TheNitek/RfidShelf/images/board/x_audioadapter.jpg

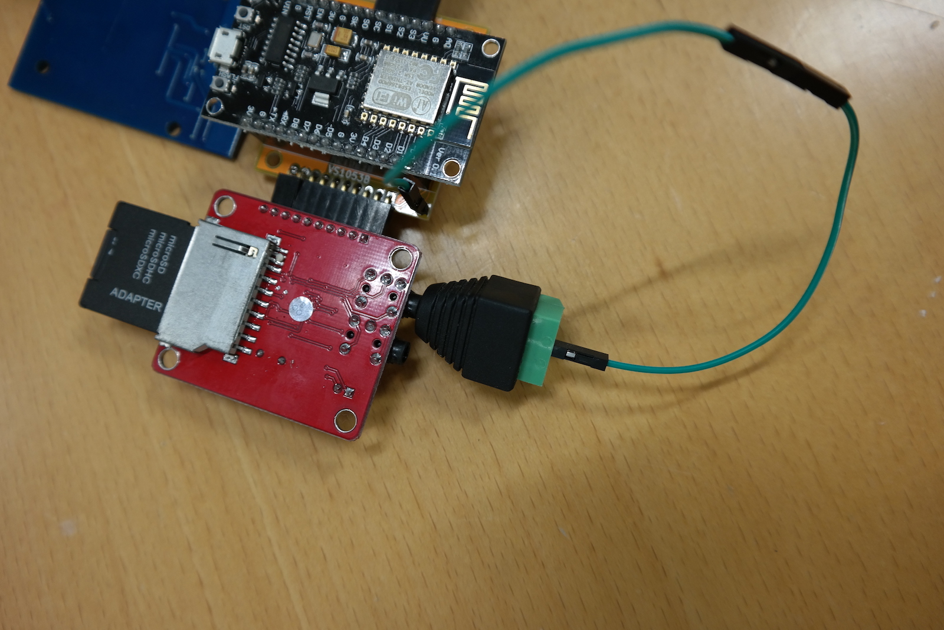
images/board/x_audioadapter.jpg
