TheNitek/RfidShelf/images/board/x_boardbottom.jpg

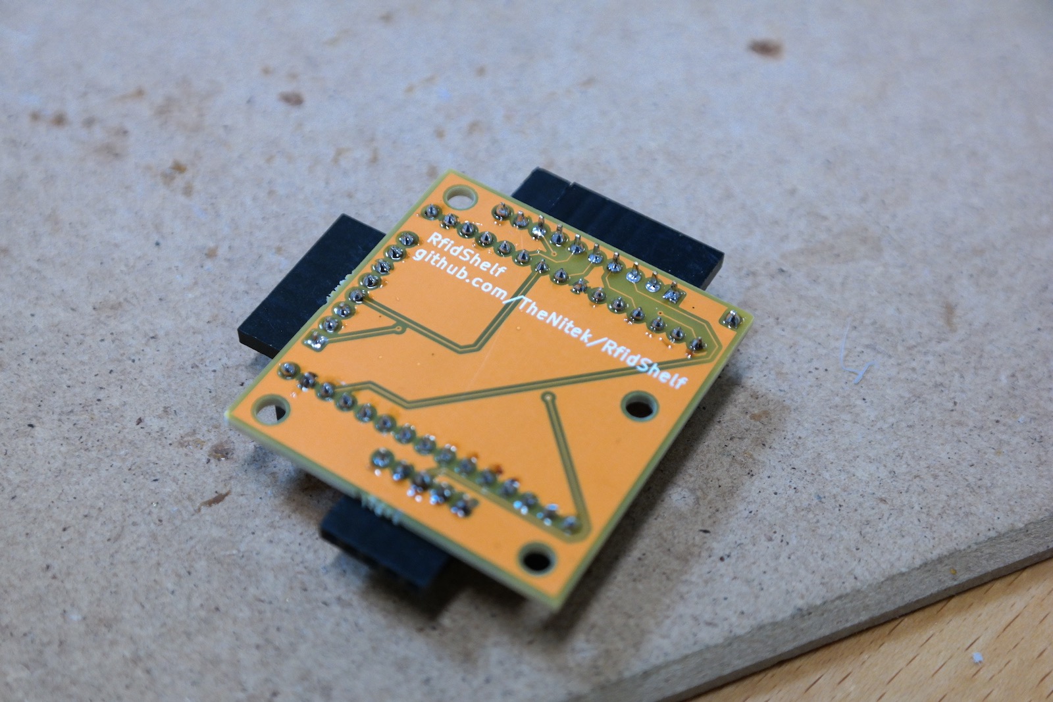
images/board/x_boardbottom.jpg
