TheNitek/RfidShelf/images/board/x_boardsbottom.jpg

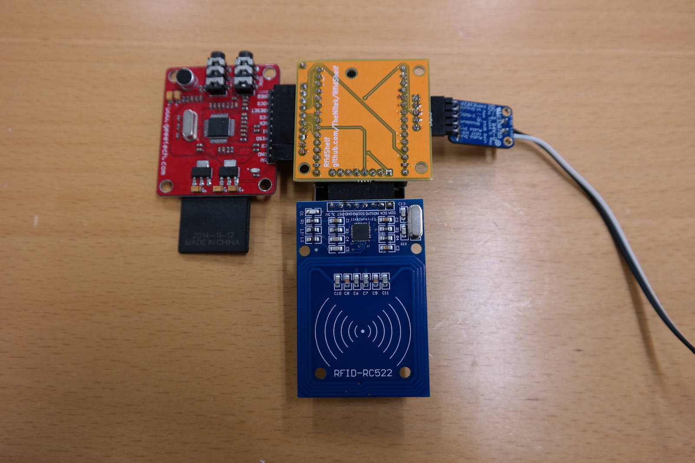
images/board/x_boardsbottom.jpg
