TheNitek/RfidShelf/images/board/x_boardstop.jpg

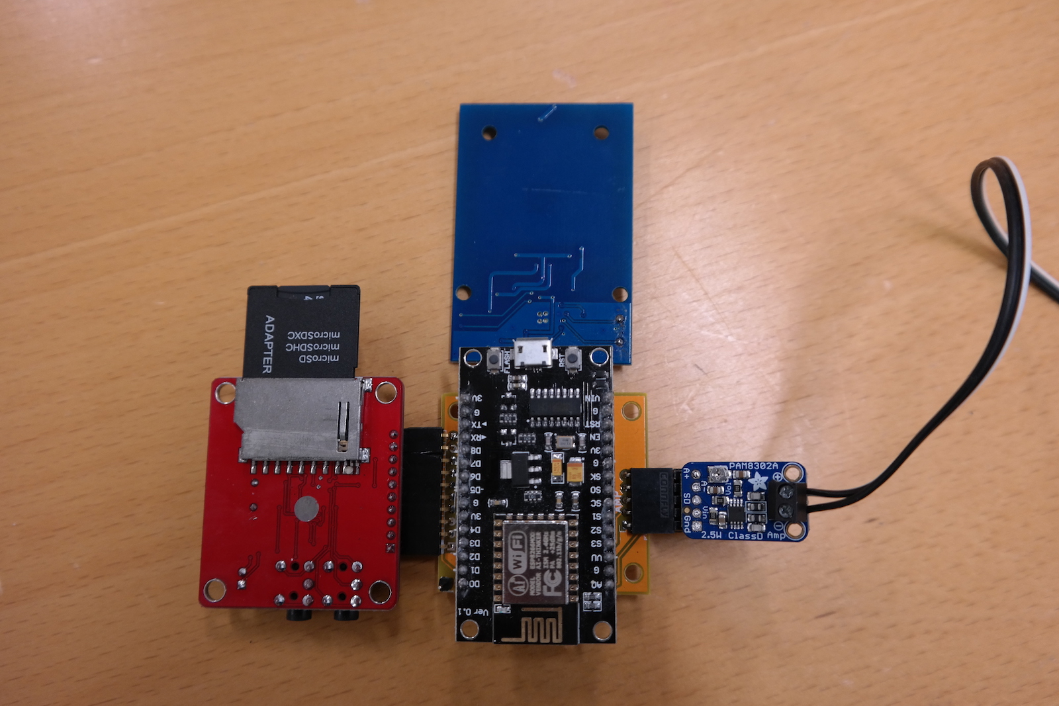
images/board/x_boardstop.jpg
