TheNitek/RfidShelf/images/board/x_boardtop.jpg

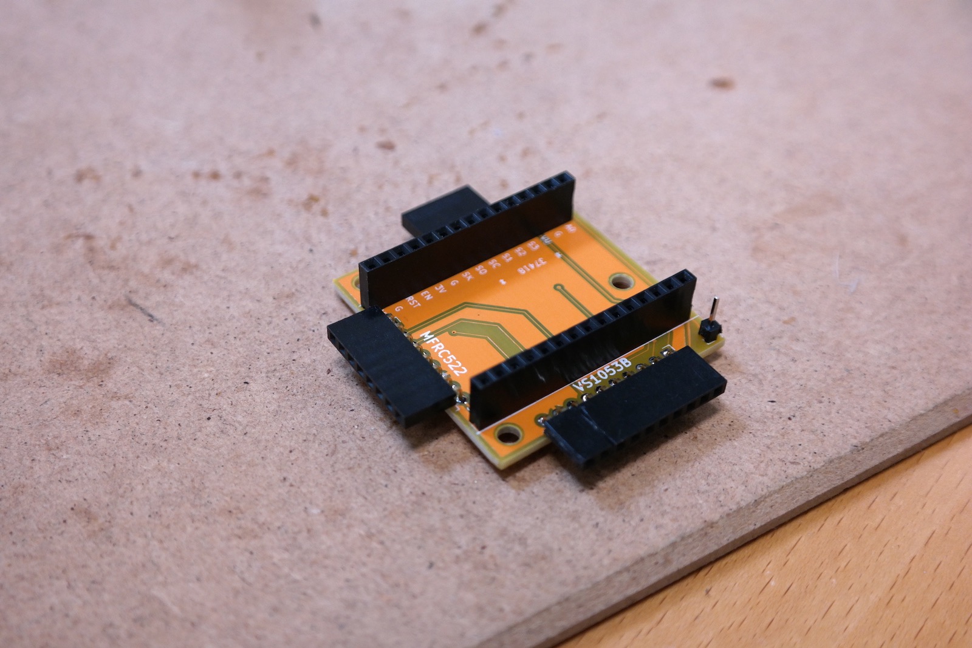
images/board/x_boardtop.jpg
