TheNitek/RfidShelf/images/board/x_audiosolder.jpg

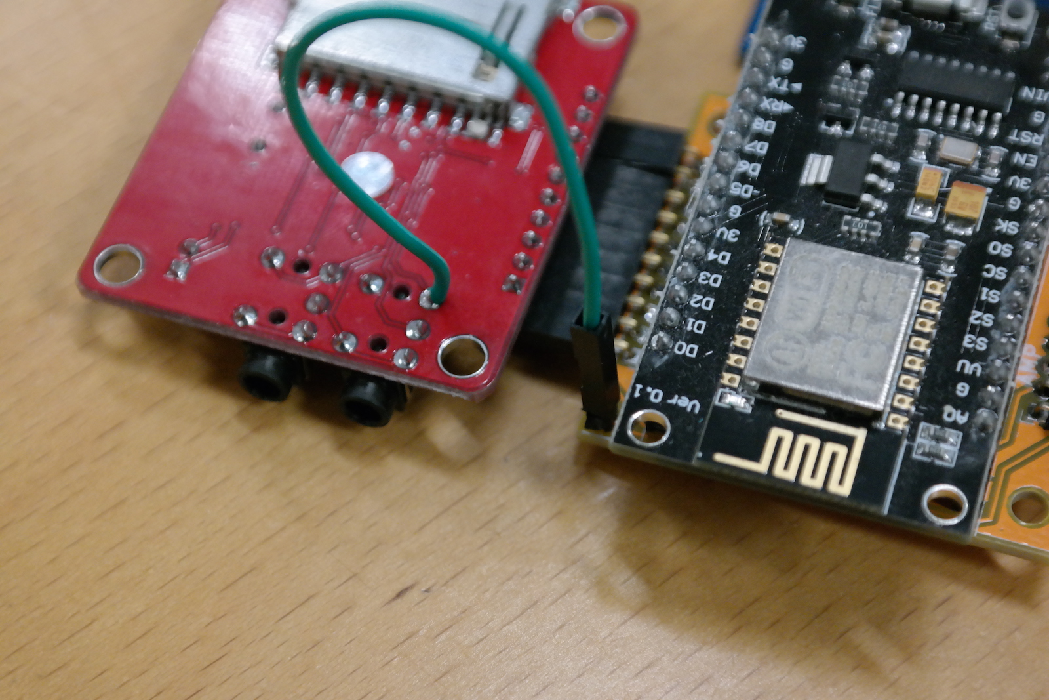
images/board/x_audiosolder.jpg
