TheNitek/RfidShelf/RfidShelf/src/ShelfRfid.cpp

#include "ShelfRfid.h"

void ShelfRfid::begin() {
  _mfrc522.PCD_Init(); // Init MFRC522 card

  Sprintln(F("RFID initialized"));
}

void ShelfRfid::handleRfid(bool ignoreTagData) {
  if ((_playback.playbackState() != ShelfPlayback::PLAYBACK_NO) && (millis() - _lastRfidCheck < 500)) {
    return;
  }
  _lastRfidCheck = millis();

  // While playing check if the tag is still present
  if ((_playback.playbackState() == ShelfPlayback::PLAYBACK_FILE)
      && _playback.playingByCard
      && (_currentCard.config.stopOnRemove == 1 || (_currentCard.config.stopOnRemove == 2 && _config.defaultStopOnRemove))) {

    // Since wireless communication is voodoo we'll give it a few retrys before killing the music
    for (int i = 0; i < 3; i++) {
      // Detect Tag without looking for collisions
      byte bufferATQA[2];
      byte bufferSize = sizeof(bufferATQA);

      MFRC522::StatusCode result = _mfrc522.PICC_WakeupA(bufferATQA, &bufferSize);

      if (result == MFRC522::STATUS_OK && _mfrc522.PICC_ReadCardSerial() && !memcmp(_mfrc522.uid.uidByte, _lastCardUid, 4)) {
        _mfrc522.PICC_HaltA();
        return;
      }
    }

    _playback.pausePlayback();
  }

  // Look for new cards and select one if it exists
  if (!_mfrc522.PICC_IsNewCardPresent() ||  !_mfrc522.PICC_ReadCardSerial()) {
    return;
  }

  if(ignoreTagData) {
    Sprintln(F("Ignoring current tag"));
    // Halt PICC
    _mfrc522.PICC_HaltA();
    // Stop encryption on PCD
    _mfrc522.PCD_StopCrypto1();
    return;
  }

  // Show some details of the PICC (that is: the tag/card)
  Sprint(F("Card UID:"));
  _print_byte_array(_mfrc522.uid.uidByte, _mfrc522.uid.size);
  Sprint(F("PICC type: "));
  MFRC522::PICC_Type piccType = _mfrc522.PICC_GetType(_mfrc522.uid.sak);
  Sprintln(_mfrc522.PICC_GetTypeName(piccType));

  // Check for compatibility
  if (piccType != MFRC522::PICC_TYPE_MIFARE_1K && piccType != MFRC522::PICC_TYPE_MIFARE_UL ) {
    Sprintln(F("Unsupported card."));
    return;
  }

  if (hasActivePairing) {
    _playback.stopPlayback();
    _writeRfidBlock(1, 0, (uint8_t*) _pairingCard.folder, strlen(_pairingCard.folder)+1);
    _writeConfigBlock(&_pairingCard.config);
    hasActivePairing = false;
  }

  // Reset watchdog timer
  ESP.wdtFeed();
  _handleRfidData();

  // Halt PICC
  _mfrc522.PICC_HaltA();
  // Stop encryption on PCD
  _mfrc522.PCD_StopCrypto1();
}

void ShelfRfid::_handleRfidData() {
  uint8_t readBuffer[18];
  /* RFID Layout:
   * Mifare Classic:
   * Sector 1, Block 0: Folder
   * Sector 2, Block 0: Config
   * 
   * Mifare Ultra:
   * Page 4-7: Folder
   * Page 8-11: Config
  */
  if (!_readRfidBlock(1, 0, readBuffer, sizeof(readBuffer))) {
    // we could not read card, skip handling
    return;
  }

  // Store uid
  memcpy(_lastCardUid, _mfrc522.uid.uidByte, 4 * sizeof(uint8_t) );

  if(readBuffer[0] == '\0') {
    return;
  }

  char readFolder[18];
  readFolder[0] = '/';
  // allthough sizeof(readBuffer) == 18, we only get 16 byte of data (2 bytes are CRC)
  memcpy(readFolder + 1 , readBuffer, 16 * sizeof(uint8_t) );
  // readBuffer will already contain \0 if the folder name is < 16 chars, but otherwise we need to add it
  readFolder[17] = '\0';

  char currentFolder[101];
  currentFolder[0] = '/';
  _playback.currentFolder(currentFolder+1, sizeof(currentFolder)-1);
  if ((_playback.playbackState() != ShelfPlayback::PLAYBACK_NO) && !strcmp(readFolder, currentFolder)) {
    Sprint(F("Resuming ")); Sprintln(currentFolder);
    _playback.resumePlayback();
    _playback.playingByCard = true;
  } else if (_playback.switchFolder(readFolder) && _handleRfidConfig()) {
    strcpy(_currentCard.folder, readFolder);
    _setPlaybackOptions(_currentCard.config.repeat, _currentCard.config.shuffle);
    _playback.startPlayback();
    _playback.playingByCard = true;
  } else {
    Sprintln(F("Ignoring card"));
    return;
  }

  _dumpCurrentCard(&_currentCard);
}

bool ShelfRfid::_handleRfidConfig() {
  uint8_t configBuffer[18];
  if (!_readRfidBlock(2, 0, configBuffer, sizeof(configBuffer))) {
    // we could not read card config, skip handling
    return false;
  }

  memcpy(&_currentCard.config, configBuffer, sizeof(CardConfig));

  if(_currentCard.config.magicByte != RFID_CONFIG_MARKER || _currentCard.config.size != 2) {
    // "Upgrade" card
    Sprintln(F("Found old version, upgrading card..."));
    _currentCard.config.size = 2;
    _currentCard.config.repeat = 2;
    _currentCard.config.shuffle = 2;
    _currentCard.config.stopOnRemove = 2;
    if(_currentCard.config.magicByte != RFID_CONFIG_MARKER || _currentCard.config.size != 1) {
      Sprintln(F("Setting magic byte and volume"));
      _currentCard.config.magicByte = RFID_CONFIG_MARKER;
      _currentCard.config.volume = _config.defaultVolumne;
    }
    _writeConfigBlock(&_currentCard.config);
  }

  Sprint(F("Setting volume: ")); Sprintln(_currentCard.config.volume);
  _playback.volume(_currentCard.config.volume);
  return true;
}


void ShelfRfid::_setPlaybackOptions(const uint8_t repeat, const uint8_t shuffle) {
  if(repeat == 1 || (repeat == 2 && _config.defaultRepeat)) {
    _playback.startRepeat();
  } else {
    _playback.stopRepeat();
  }
  
  if(shuffle == 1 || (shuffle == 2 && _config.defaultShuffle)) {
    _playback.startShuffle();
  } else {
    _playback.stopShuffle();
  }
}

ShelfRfid::NFCTagObject ShelfRfid::getPairingConfig() {
  return _pairingCard;
}

bool ShelfRfid::startPairing(const char *folder, const uint8_t volume, const uint8_t repeat, const uint8_t shuffle, const uint8_t stopOnRemove) {
  if(strlen(folder) > 16 || repeat > 2 || shuffle > 2 || stopOnRemove > 2)
    return false;
  
  strcpy(_pairingCard.folder, folder);
  _pairingCard.config.magicByte = RFID_CONFIG_MARKER;
  _pairingCard.config.size = 2;
  _pairingCard.config.volume = volume;
  _pairingCard.config.repeat = repeat;
  _pairingCard.config.shuffle = shuffle;
  _pairingCard.config.stopOnRemove = stopOnRemove;

  Sprintln(F("Pairing mode enabled"));
  _dumpCurrentCard(&_pairingCard);

  hasActivePairing = true;
  return true;
}

void ShelfRfid::_dumpCurrentCard(const NFCTagObject *card) {
  Sprintln(F("Current card data: "));
  Sprint(F("  folder: ")); Sprintln(card->folder);
  Sprint(F("  volume: ")); Sprintln(card->config.volume);
  Sprint(F("  repeat: ")); Sprintln(card->config.repeat);
  Sprint(F("  shuffle: ")); Sprintln(card->config.shuffle);
  Sprint(F("  stopOnRemove: ")); Sprintln(card->config.stopOnRemove);
}

void ShelfRfid::_writeConfigBlock(const CardConfig *config) {

  // Store config (like volume)
  uint8_t configBuffer[sizeof(CardConfig)];

  memcpy(configBuffer, config, sizeof(CardConfig));
  _writeRfidBlock(2, 0, configBuffer, sizeof(CardConfig));
}

bool ShelfRfid::_writeRfidBlock(const uint8_t sector, const uint8_t relativeBlock, const uint8_t *content, const uint8_t contentSize) {
  uint8_t absoluteBlock = (sector * 4) + relativeBlock;
  MFRC522::StatusCode status;
  MFRC522::PICC_Type piccType = _mfrc522.PICC_GetType(_mfrc522.uid.sak);

  if(piccType == MFRC522::PICC_TYPE_MIFARE_1K) {
      // Authenticate using key A
    Sprintln(F("Authenticating using key A..."));
    status = _mfrc522.PCD_Authenticate(MFRC522::PICC_CMD_MF_AUTH_KEY_A, absoluteBlock, &_key, &(_mfrc522.uid));
    if (status != MFRC522::STATUS_OK) {
      Sprint(F("PCD_Authenticate() failed: "));
      Sprintln(_mfrc522.GetStatusCodeName(status));
      return false;
    }
  }

  const uint8_t bufferSize = 16;
  byte buffer[bufferSize];

  uint8_t blockSize = 16;
  if(piccType == MFRC522::PICC_TYPE_MIFARE_UL) {
    blockSize = 4;
  }

  // While reading works basically the same for Mifare Classic and Ultra, Ultras need to be written in chunks of 4 bytes instead of 16
  Sprint(F("Writing data: ")); _print_byte_array(content, contentSize);
  for(uint8_t i = 0; (i < 16/blockSize) && (i*blockSize < contentSize); i++) {
    // Write block
    memset(buffer, 0, bufferSize * sizeof(uint8_t));
    memcpy(buffer, content+(i*blockSize), (((i+1)*blockSize > contentSize) ? (contentSize % blockSize) : blockSize) * sizeof(uint8_t) );

    status = _mfrc522.MIFARE_Write(absoluteBlock + i, buffer, bufferSize);
    if (status != MFRC522::STATUS_OK) {
      Sprint(F("MIFARE_Write() failed: ")); Sprintln(_mfrc522.GetStatusCodeName(status));
      return false;
    }
  }
  return true;
}

/**
   read a block from a rfid card into outputBuffer which needs to be >= 18 bytes long
*/
bool ShelfRfid::_readRfidBlock(uint8_t sector, uint8_t relativeBlock, uint8_t *outputBuffer, uint8_t bufferSize) {
  if (relativeBlock > 3) {
    Sprintln(F("Invalid block number"));
    return false;
  }

  uint8_t absoluteBlock = (sector * 4) + relativeBlock;
  MFRC522::StatusCode status;
  MFRC522::PICC_Type piccType = _mfrc522.PICC_GetType(_mfrc522.uid.sak);

  if(piccType == MFRC522::PICC_TYPE_MIFARE_1K) {
    // Authenticate using key A
    Sprintln(F("Authenticating using key A..."));
    status = _mfrc522.PCD_Authenticate(MFRC522::PICC_CMD_MF_AUTH_KEY_A, absoluteBlock, &_key, &(_mfrc522.uid));
    if (status != MFRC522::STATUS_OK) {
      Sprint(F("PCD_Authenticate() failed: "));
      Sprintln(_mfrc522.GetStatusCodeName(status));
      return false;
    }
  }

  Sprint(F("Reading block ")); Sprint(absoluteBlock); Sprintln(F(":"));
  status = _mfrc522.MIFARE_Read(absoluteBlock, outputBuffer, &bufferSize);
  if (status != MFRC522::STATUS_OK) {
    Sprint(F("MIFARE_Read() failed: ")); Sprintln(_mfrc522.GetStatusCodeName(status));
    return false;
  }
  _print_byte_array(outputBuffer, 16);
  Sprintln();
  Sprintln();

  return true;
}


void ShelfRfid::_print_byte_array(const uint8_t *buffer, const uint8_t  bufferSize) {
#ifdef DEBUG_ENABLE
  for (uint8_t i = 0; i < bufferSize; i++) {
    Sprint(buffer[i] < 0x10 ? " 0" : " ");
    // Use Serial.print here because of HEX parameter and ifdef around this
    Serial.print(buffer[i], HEX);
  }
  Sprintln();
#endif
}
