TheNitek/RfidShelf/RfidShelf/ShelfWeb.cpp

#include "ShelfWeb.h"

void ShelfWeb::begin() {
  std::function<void(void)> defaultCallback = std::bind(&ShelfWeb::_handleDefault, this);
  _server.on(
    "/",
    HTTP_POST,
    defaultCallback,
    std::bind(&ShelfWeb::_handleFileUpload, this)
  );
  _server.onNotFound(defaultCallback);
  // Done by espalexa
  //_server.begin();

  DeviceCallbackFunction deviceCallback = std::bind(&ShelfWeb::_deviceCallback, this, std::placeholders::_1);
  _alexaDevice = new EspalexaDevice(_config.hostname, deviceCallback, EspalexaDeviceType::dimmable, 50);
  _alexaDevice->setPercent(2*(50-_playback.volume()));
  _espalexa.addDevice(_alexaDevice);
  _espalexa.begin(&_server);

  PlaybackCallbackFunction playbackCallback = std::bind(&ShelfWeb::_playbackCallback, this, std::placeholders::_1, std::placeholders::_2);
  _playback.callback = playbackCallback;

  MDNS.addService("http", "tcp", 80);
}

void ShelfWeb::_deviceCallback(EspalexaDevice* device) {
  Sprintf("Got device callback type: %d\n", device->getLastChangedProperty());

  switch(device->getLastChangedProperty()) {
    case EspalexaDeviceProperty::off:
      if(_playback.playbackState() == PLAYBACK_FILE) {
        _playback.pausePlayback();
      }
      break;
    case EspalexaDeviceProperty::on: 
      if(_playback.playbackState() == PLAYBACK_PAUSED) {
        _playback.playingByCard = false;
        _playback.resumePlayback();
        device->setPercent(2*(50-_playback.volume()));
      }
      break;
    case EspalexaDeviceProperty::bri:
      _playback.volume(50-device->getPercent()/2, false);
      break;
    default:
      Sprintln("Callback ignored");
  }
}

void ShelfWeb::_playbackCallback(PlaybackState state, uint8_t volume) {
  if(state == PLAYBACK_FILE) {
    _alexaDevice->setPercent(2*(50-_playback.volume()));
  } else {
    _alexaDevice->setValue(0);
  }
}

void ShelfWeb::_returnOK() {
  _server.send_P(200, "text/plain", NULL);
}

void ShelfWeb::_returnHttpStatus(uint16_t statusCode, const char *msg) {
  _server.send_P(statusCode, "text/plain", msg);
}

void ShelfWeb::_sendHTML() {
  _server.sendHeader("Content-Encoding", "gzip");
  _server.send_P(200, "text/html", ShelfHtml::INDEX, ShelfHtml::INDEX_SIZE);
}

void ShelfWeb::_sendJsonStatus() {
  char output[768] = "{\"playback\":\"";
  char buffer[101];

  if(_playback.playbackState() == PLAYBACK_FILE) {
    strcat(output, "FILE\"");
  } else if(_playback.playbackState() == PLAYBACK_PAUSED) {
    strcat(output, "PAUSED\"");
  } else {
    strcat(output, "NO\"");
  }

  if(_rfid.hasActivePairing) {
    nfcTagObject pairingConfig = _rfid.getPairingConfig();
    strcat(output, ",\"pairing\":\"");
    strcat(output, pairingConfig.folder);
    strcat(output, "\"");
  }

  if(_playback.playbackState() != PLAYBACK_NO) {
    _playback.currentFile(buffer, sizeof(buffer));
    strcat(output, ",\"currentFile\":\"");
    strcat(output, buffer);
    _playback.currentFolder(buffer, sizeof(buffer));
    strcat(output, "\",\"currentFolder\":\"");
    strcat(output, buffer);
    strcat(output, "\"");
  }

  strcat(output, ",\"volume\":");
  snprintf(buffer, sizeof(buffer), "%d", 50 - _playback.volume());
  strcat(output, buffer);

  if (_SD.exists("/patches.053")) {
    strcat(output, ",\"patch\":true");
  } else {
    strcat(output, ",\"patch\":false");
  }

  if(_playback.isNight()) {
    strcat(output, ",\"night\":true");
  } else {
    strcat(output, ",\"night\":false");
  }

  if(_playback.isShuffle()) {
    strcat(output, ",\"shuffle\":true");
  } else {
    strcat(output, ",\"shuffle\":false");
  }

  strcat(output, ",\"time\":");
  snprintf(buffer, sizeof(buffer), "%lu", time(nullptr));
  strcat(output, buffer);

  strcat(output, ",\"version\":");
  snprintf(buffer, sizeof(buffer), "\"%d.%d\"", MAJOR_VERSION, MINOR_VERSION);
  strcat(output, buffer);
  strcat(output, "}");

  _server.send_P(200, "application/json", output);
}

void ShelfWeb::_sendJsonFSUsage() {
  uint32_t free = (uint32_t)(0.000512*_SD.vol()->freeClusterCount()*_SD.vol()->blocksPerCluster());
  uint32_t total = (uint32_t)(0.000512*_SD.card()->cardCapacity());

  // This is too slow on bigger cards, so it needs to be moved somewhere else
  char output[51] = "";
  snprintf(output, sizeof(output), "{\"free\":%u,\"total\":%u}", free, total);
  _server.send_P(200, "application/json", output);
}

void ShelfWeb::_sendJsonConfig() {
  char output[768] = "{\"host\":\"";
  char buffer[101];

  strcat(output, _config.hostname);
  strcat(output, "\",\"ntp\":\"");
  strcat(output, _config.ntpServer);
  strcat(output, "\",\"tz\":\"");
  strcat(output, _config.timezone);
  strcat(output, "\",\"volume\":");
  snprintf(buffer, sizeof(buffer), "%d", _config.defaultVolumne);
  strcat(output, buffer);
  strcat(output, ",\"repeat\":");
  strcat(output, _config.defaultRepeat ? "true" : "false");
  strcat(output, ",\"shuffle\":");
  strcat(output, _config.defaultShuffle ? "true" : "false");
  strcat(output, ",\"stopOnRemove\":");
  strcat(output, _config.defaultStopOnRemove ? "true" : "false");
  strcat(output, ",\"nightMode\":[");
  for(uint8_t i = 0; i < sizeof(_config.nightModeTimes)/sizeof(Timeslot_t); i++) {
    strcat(output, "{");
    strcat(output, "\"days\":[");
    strcat(output, _config.nightModeTimes[i].monday ? "true," : "false,");
    strcat(output, _config.nightModeTimes[i].tuesday ? "true," : "false,");
    strcat(output, _config.nightModeTimes[i].wednesday ? "true," : "false,");
    strcat(output, _config.nightModeTimes[i].thursday ? "true," : "false,");
    strcat(output, _config.nightModeTimes[i].friday ? "true," : "false,");
    strcat(output, _config.nightModeTimes[i].saturday ? "true," : "false,");
    strcat(output, _config.nightModeTimes[i].sunday ? "true" : "false");
    strcat(output, "],\"start\":\"");
    snprintf(buffer, sizeof(buffer), "%02d:%02d", _config.nightModeTimes[i].startHour, _config.nightModeTimes[i].startMinutes);
    strcat(output, buffer);
    strcat(output, "\",\"end\":\"");
    snprintf(buffer, sizeof(buffer), "%02d:%02d", _config.nightModeTimes[i].endHour, _config.nightModeTimes[i].endMinutes);
    strcat(output, buffer);
    strcat(output, "\"");

    strcat(output, "}");
    if(i < sizeof(_config.nightModeTimes)/sizeof(Timeslot_t) - 1) {
      strcat(output, ",");
    }
  }
  strcat(output, "]}");

  _server.send_P(200, "application/json", output);
}

void ShelfWeb::_sendJsonFS(const char *path) {
  _server.setContentLength(CONTENT_LENGTH_UNKNOWN);
  _server.send_P(200, "application/json", "{\"fs\":[");

  sdfat::SdFile dir;
  dir.open(path, sdfat::O_READ);

  sdfat::SdFile entry;

  char buffer[101];
  char output[256];

  bool first = true;

  while (entry.openNext(&dir, sdfat::O_READ)) {
    if(first) {
      first = false;
      strcpy(output, "{\"name\":\"");
    } else {
      strcpy(output, ",{\"name\":\"");
    }
    entry.getName(buffer, sizeof(buffer));
    // TODO encode special characters
    strcat(output, buffer);
    if (entry.isDir()) {
      strcat(output, "\"");
    } else {
      strcat(output, "\",\"size\":");
      snprintf(buffer, sizeof(buffer), "%lu", (unsigned long) entry.fileSize());
      strcat(output, buffer);
    }
    entry.close();
    strcat(output, "}");
    _server.sendContent_P(output);
  }
  _server.sendContent_P("],");
  snprintf(output, sizeof(output), "\"path\":\"%s\"", path);
  _server.sendContent_P(output);
  _server.sendContent_P("}");
  _server.sendContent_P("");

  dir.close();
}

bool ShelfWeb::_loadFromSdCard(const char *path) {
  sdfat::File dataFile = _SD.open(path);

  if (!dataFile) {
    Sprintln("File not open");
    _returnHttpStatus(404, "Not found");
    return false;
  }

  if (dataFile.isDir()) {
    _sendJsonFS(path);
  } else {
    if (_server.streamFile(dataFile, "application/octet-stream") != dataFile.size()) {
      Sprintln("Sent less data than expected!");
    }
  }
  dataFile.close();
  return true;
}

void ShelfWeb::_downloadPatch() {
  Sprintln("Starting patch download");
  std::unique_ptr<BearSSL::WiFiClientSecure>client(new BearSSL::WiFiClientSecure);
  // do not validate certificate
  client->setInsecure();
  HTTPClient httpClient;
  httpClient.begin(*client, VS1053_PATCH_URL);
  int httpCode = httpClient.GET();
  if (httpCode < 0) {
    httpClient.end();
    _returnHttpStatus(500, httpClient.errorToString(httpCode).c_str());
    return;
  }
  if (httpCode != HTTP_CODE_OK) {
    httpClient.end();
    char buffer[32];
    snprintf(buffer, sizeof(buffer), "invalid response code: %d", httpCode);
    _returnHttpStatus(500, buffer);
    return;
  }

  sdfat::File patchFile("/patches.053",sdfat::O_WRITE | sdfat::O_CREAT);
  if(!patchFile.isOpen()) {
    httpClient.end();
    _returnHttpStatus(500, "Could not open patch file");
    return;
  }
  patchFile.close();
  _returnOK();
  _server.client().flush();
  ESP.restart();
}

void ShelfWeb::_handleFileUpload() {
  // Upload always happens on /
  if (_server.uri() != "/") {
    Sprintln("Invalid upload URI");
    return;
  }

  HTTPUpload& upload = _server.upload();

  if (upload.status == UPLOAD_FILE_START) {
    String filename = upload.filename;

    if (!filename.startsWith("/")) {
      Sprintln("Invalid upload target");
      return;
    }

    if (_SD.exists(filename.c_str())) {
      Sprintln("File " + filename + " already exists. Skipping");
      return;
    }

    if(_playback.playbackState() == PLAYBACK_FILE) {
      Sprintln("Pausing playback for upload");
      _playback.pausePlayback();
    }

    _uploadFile.open(filename.c_str(), sdfat::O_WRITE | sdfat::O_CREAT);
    _uploadStart = millis();
    Sprint("Upload start: ");
    Sprintln(filename);
  } else if (upload.status == UPLOAD_FILE_WRITE) {
    if (_uploadFile.isOpen()) {
      _uploadFile.write(upload.buf, upload.currentSize);
      //Sprint("Upload write: "));
      //Sprintln(upload.currentSize);
    }
  } else if (upload.status == UPLOAD_FILE_END) {
    if (_uploadFile.isOpen()) {
      _uploadFile.close();
      Sprint("Upload end: "); Sprintln(upload.totalSize);
      Sprint("Took: "); Sprintln(((millis()-_uploadStart)/1000));
    }
  }
}

void ShelfWeb::_handleDefault() {
  String path = _server.urlDecode(_server.uri());
  Sprintf("Request to: %s\n", path.c_str());
  if(_espalexa.handleAlexaApiCall(_server.uri(), _server.arg("plain"))) {
    return;
  }
  if(_server.method() == HTTP_GET) {
    if(_server.hasArg("status")) {
      _sendJsonStatus();
      return;
    }
    if(_server.hasArg("config")) {
      _sendJsonConfig();
      return;
    }
    if(_server.hasArg("usage")) {
      _sendJsonFSUsage();
      return;
    }
    if(path == "/" && !_server.hasArg("fs")) {
      _sendHTML();
      return;
    }

    // start file download
    _loadFromSdCard(path.c_str());
    return;
  } else if(_server.method() == HTTP_DELETE) {
    if(path == "/" || !_SD.exists(path.c_str())) {
      _returnHttpStatus(400, "Bad path");
      return;
    }

    sdfat::SdFile file;
    file.open(path.c_str());
    if(file.isDir()) {
      if(!file.rmRfStar()) {
        Sprintln("Could not delete folder");
      }
    } else {
      if(!_SD.remove(path.c_str())) {
        Sprintln("Could not delete file");
      }
    }
    file.close();
    _returnOK();
    return;
  } else if(_server.method() == HTTP_POST) {
    if(_server.hasArg("newFolder")) {
      Sprint("Creating folder "); Sprintln(_server.arg("newFolder"));
      if(_SD.mkdir(_server.arg("newFolder").c_str())) {
        _SD.cacheClear();
        _returnOK();
      } else {
        Sprintln("Folder creation failed");
        _returnHttpStatus(500, "Folder creation failed");
      }
      return;
    } else if(_server.hasArg("ota")) {
      Sprint("Starting OTA from "); Sprintln(_server.arg("ota"));
      std::unique_ptr<BearSSL::WiFiClientSecure>client(new BearSSL::WiFiClientSecure);
      // do not validate certificate
      client->setInsecure();
      t_httpUpdate_return ret = ESPhttpUpdate.update(*client, _server.arg("ota"));
      switch (ret) {
        case HTTP_UPDATE_FAILED:
          Sprintf("HTTP_UPDATE_FAILD Error (%d): ", ESPhttpUpdate.getLastError());
          Sprintln(ESPhttpUpdate.getLastErrorString().c_str());
          _returnHttpStatus(500, "Update failed, please try again");
          return;
        case HTTP_UPDATE_NO_UPDATES:
          Sprintln("HTTP_UPDATE_NO_UPDATES");
          break;
        case HTTP_UPDATE_OK:
          Sprintln("HTTP_UPDATE_OK");
          break;
      }
      _returnOK();
      return;
    } else if(_server.hasArg("downloadpatch")) {
      _downloadPatch();
      return;
    } else if(_server.hasArg("stop")) {
      _playback.stopPlayback();
      _sendJsonStatus();
      return;
    } else if(_server.hasArg("pause")) {
      _playback.pausePlayback();
      _sendJsonStatus();
      return;
    } else if(_server.hasArg("resume")) {
      _playback.playingByCard = false;
      _playback.resumePlayback();
      _sendJsonStatus();
      return;
    } else if(_server.hasArg("skip")) {
      _playback.playingByCard = false;
      _playback.skipFile();
      _sendJsonStatus();
      return;
    } else if(_server.hasArg("volumeUp")) {
      _playback.volumeUp();
      _sendJsonStatus();
      return;
    } else if(_server.hasArg("volumeDown")) {
      _playback.volumeDown();
      _sendJsonStatus();
      return;
    } else if(_server.hasArg("toggleNight")) {
      if(_playback.isNight()) {
        _playback.stopNight();
      } else {
        _playback.startNight();
      }
      _sendJsonStatus();
      return;
    } else if(_server.hasArg("toggleShuffle")) {
      if(_playback.isShuffle()) {
        _playback.stopShuffle();
      } else {
        _playback.startShuffle();
      }
      _sendJsonStatus();
      return;
    } else if(_server.uri() == "/") {
      Sprintln("Probably got an upload request");
      _returnOK();
      return;
    } else if(_SD.exists(path.c_str())) {
      // <= 17 here because leading "/"" is included
      if(_server.hasArg("write") && path.length() <= 17) {
        const char *target = path.c_str();
        const uint8_t volume = 50-(uint8_t)_server.arg("volume").toInt();
        uint8_t repeat = _server.arg("repeat").toInt();
        uint8_t shuffle = _server.arg("shuffle").toInt();
        uint8_t stopOnRemove = _server.arg("stopOnRemove").toInt();
        // Remove leading "/""
        target++;
        if(_rfid.startPairing(target, volume, repeat, shuffle, stopOnRemove)) {
          _sendJsonStatus();
          return;
        }
      } else if(_server.hasArg("play") && _playback.switchFolder(path.c_str())) {
        _playback.startPlayback();
        _playback.playingByCard = false;
        _sendJsonStatus();
        return;
      } else if(_server.hasArg("playfile")) {
        char* pathCStr = (char *)path.c_str();
        char* folderRaw = strtok(pathCStr, "/");
        char* file = strtok(NULL, "/");

        if((folderRaw != NULL) && (file != NULL) && strlen(folderRaw) < 90) {

          char folder[100] = "/";
          strcat(folder, folderRaw);
          strcat(folder, "/");

          if(_playback.switchFolder(folder)) {
            _playback.startFilePlayback(folderRaw, file);
            _playback.playingByCard = false;
            _sendJsonStatus();
            return;
          }
        }
      }
    }
  }

  // 404 otherwise
  _returnHttpStatus(404, "Not found");
  Sprintln("404: " + path);
}

bool ShelfWeb::isFileUploading() {
  return _uploadFile.isOpen();
}

void ShelfWeb::pause() {
  _paused = true;
  _server.stop();
}

void ShelfWeb::unpause() {
  _paused = false;
  _server.begin();
}

void ShelfWeb::work() {
  if(_paused) {
    return;
  }
  // Not needed because espalexa does it
  //_server.handleClient();
  _espalexa.loop();
}
